LeandraChristine/voidnet_viator/3d_files/FDM/Optical_Mouse_Cover.stl

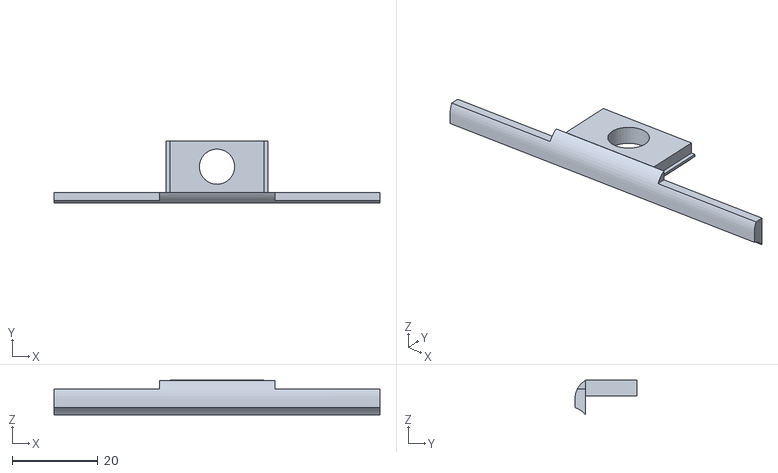
[picture p15: CAD file, 2022-09-26]
3d_files/FDM/Optical_Mouse_Cover.stl
76.0 x 14.5 x 8.09
