LeandraChristine/voidnet_viator/3d_files/FDM/Optical_Mouse_Casing.stl

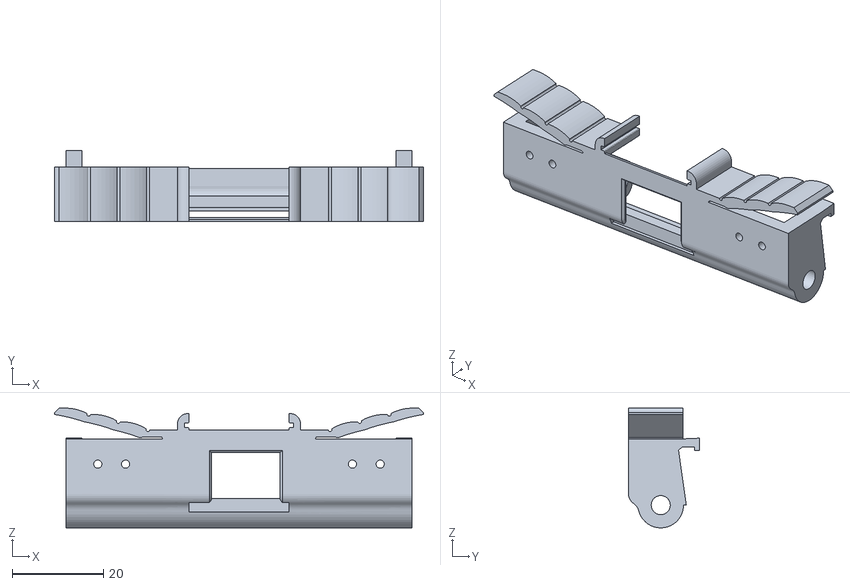
[picture p16: CAD file, 2022-09-26]
3d_files/FDM/Optical_Mouse_Casing.stl
81.0 x 15.6 x 26.3
