LeandraChristine/voidnet_viator/3d_files/FDM/Backplate_1.stl

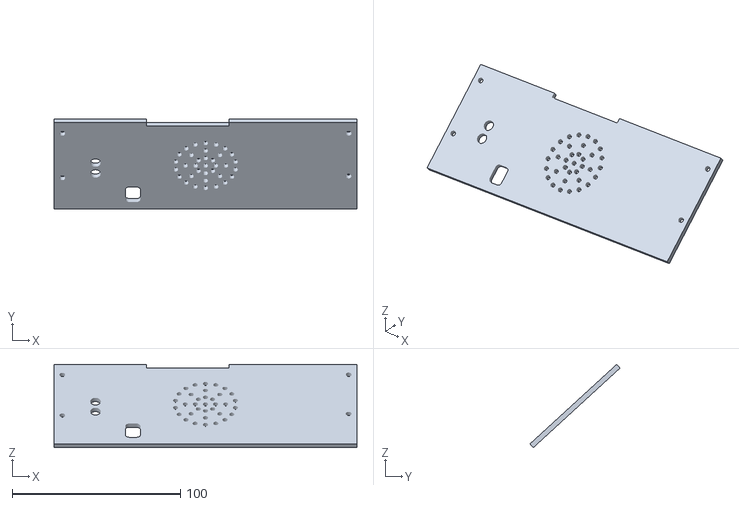
[picture p17: CAD file, 2022-09-26]
3d_files/FDM/Backplate_1.stl
179.9 x 53.5 x 49.4
