LeandraChristine/voidnet_viator/3d_files/FDM/Extension_Top.stl

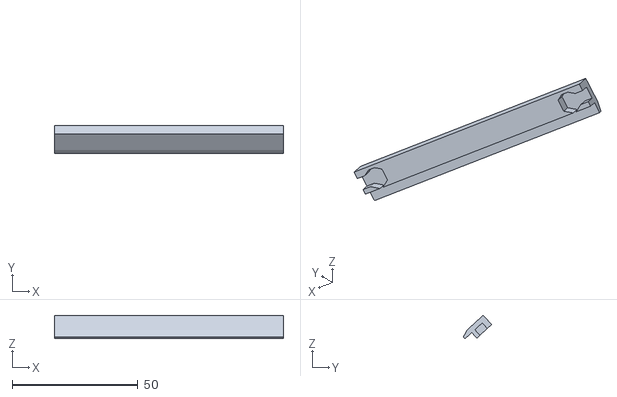
[picture p18: CAD file, 2022-09-26]
3d_files/FDM/Extension_Top.stl
91.2 x 11.3 x 9.35
