LeandraChristine/voidnet_viator/3d_files/FDM/Grip_Holder_Back.stl

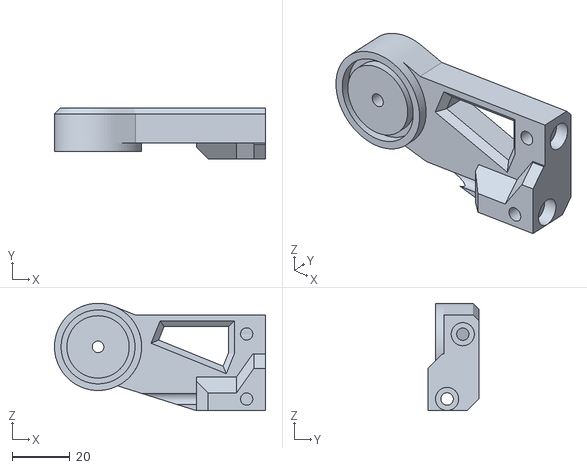
[picture p19: CAD file, 2022-09-26]
3d_files/FDM/Grip_Holder_Back.stl
72.8 x 17.5 x 37.0
