LeandraChristine/voidnet_viator/3d_files/FDM/Drillguide_Right.stl

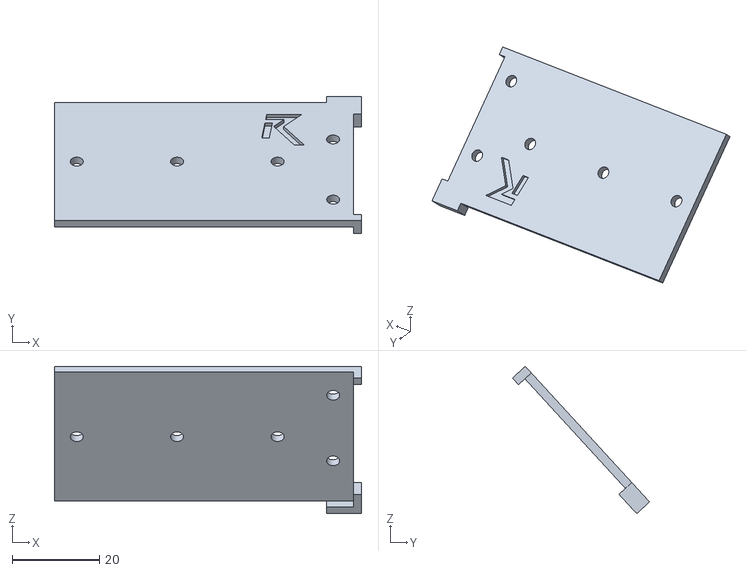
[picture p20: CAD file, 2022-09-26]
3d_files/FDM/Drillguide_Right.stl
70.2 x 31.4 x 33.7
