LeandraChristine/voidnet_viator/3d_files/FDM/Left_Front_Holder.stl

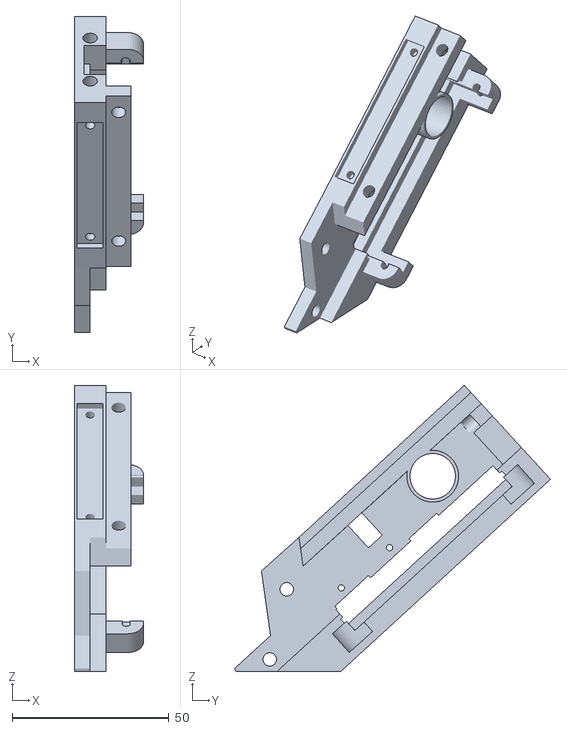
[picture p21: CAD file, 2022-09-26]
3d_files/FDM/Left_Front_Holder.stl
22.0 x 100.7 x 91.3
