LeandraChristine/voidnet_viator/3d_files/FDM/Back_Attachment_Left.stl

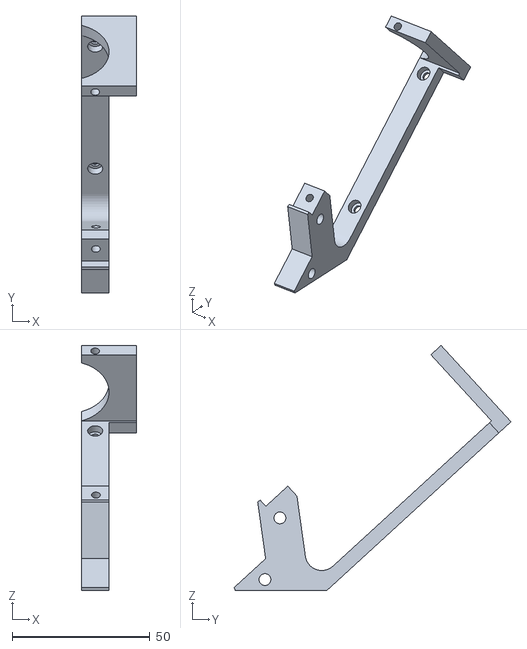
[picture p22: CAD file, 2022-09-26]
3d_files/FDM/Back_Attachment_Left.stl
20.0 x 100.4 x 88.8
