LeandraChristine/voidnet_viator/3d_files/FDM/Left_Panel.stl

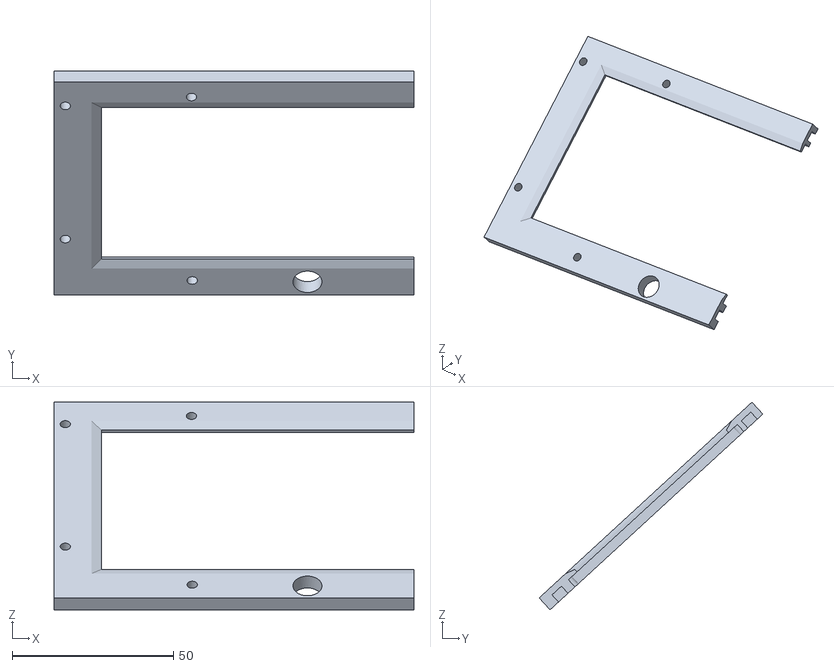
[picture p23: CAD file, 2022-09-26]
3d_files/FDM/Left_Panel.stl
111.5 x 69.3 x 64.3
