LeandraChristine/voidnet_viator/3d_files/FDM/Display_Panel.stl

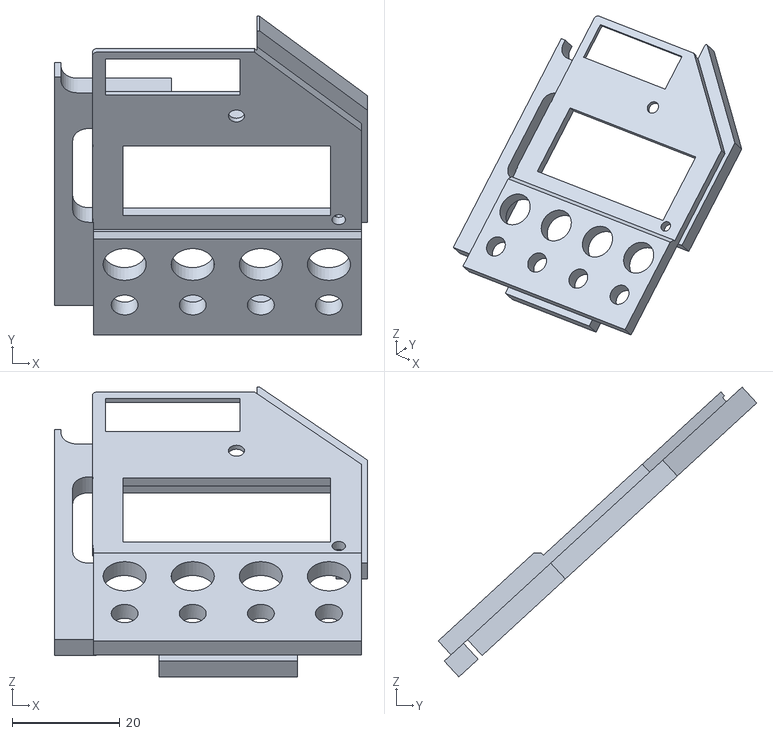
[picture p24: CAD file, 2022-09-26]
3d_files/FDM/Display_Panel.stl
58.0 x 59.0 x 53.7
