LeandraChristine/voidnet_viator/3d_files/FDM/Right_Panel.stl

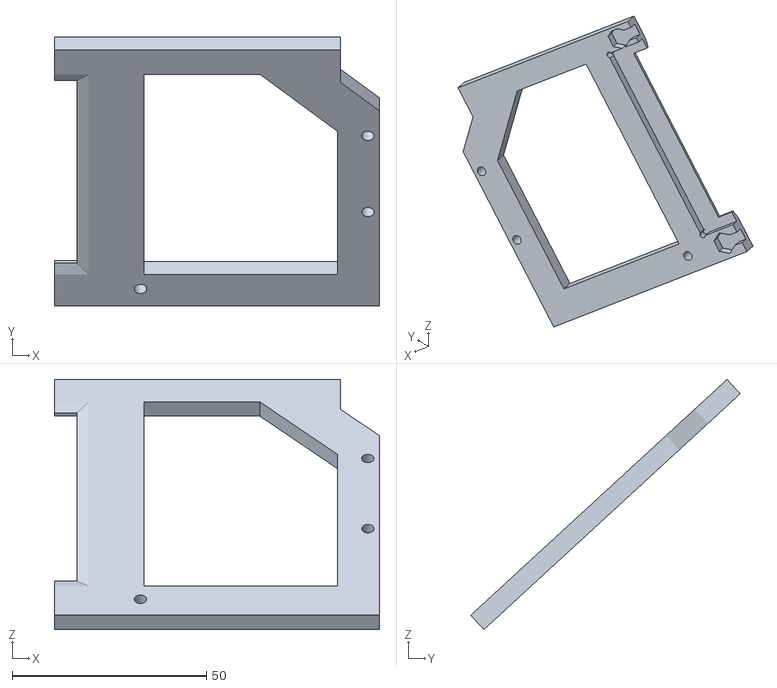
[picture p25: CAD file, 2022-09-26]
3d_files/FDM/Right_Panel.stl
83.6 x 69.3 x 64.3
