LeandraChristine/voidnet_viator/3d_files/FDM/Backplate_3.stl

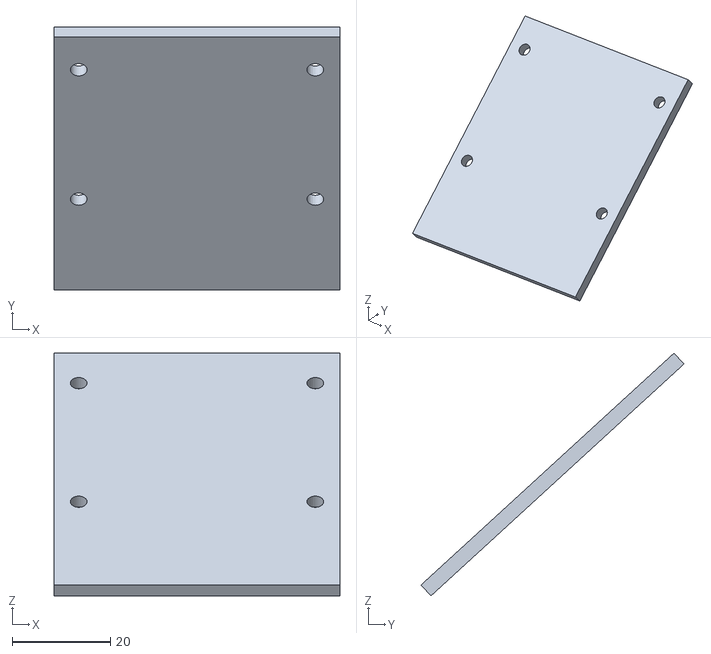
[picture p26: CAD file, 2022-09-26]
3d_files/FDM/Backplate_3.stl
58.2 x 53.5 x 49.4
