LeandraChristine/voidnet_viator/3d_files/FDM/Grip_Holder_Front.stl

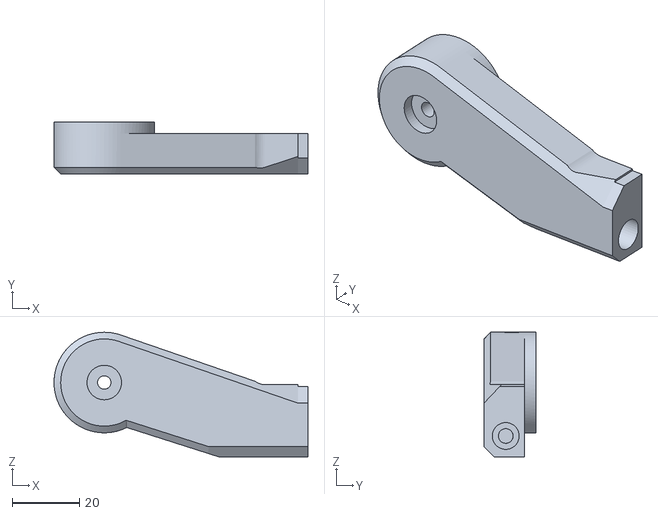
[picture p27: CAD file, 2022-09-26]
3d_files/FDM/Grip_Holder_Front.stl
75.7 x 15.5 x 37.1
