LeandraChristine/voidnet_viator/3d_files/FDM/FrontPanel_Clip.stl

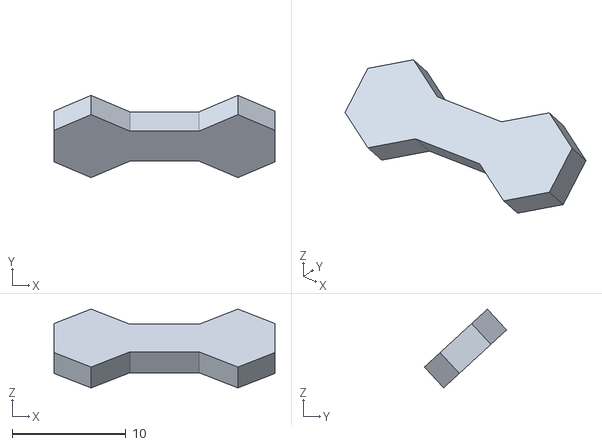
[picture p28: CAD file, 2022-09-26]
3d_files/FDM/FrontPanel_Clip.stl
19.5 x 7.24 x 6.94
