LeandraChristine/voidnet_viator/3d_files/FDM/Cable_Clamp_Top.stl

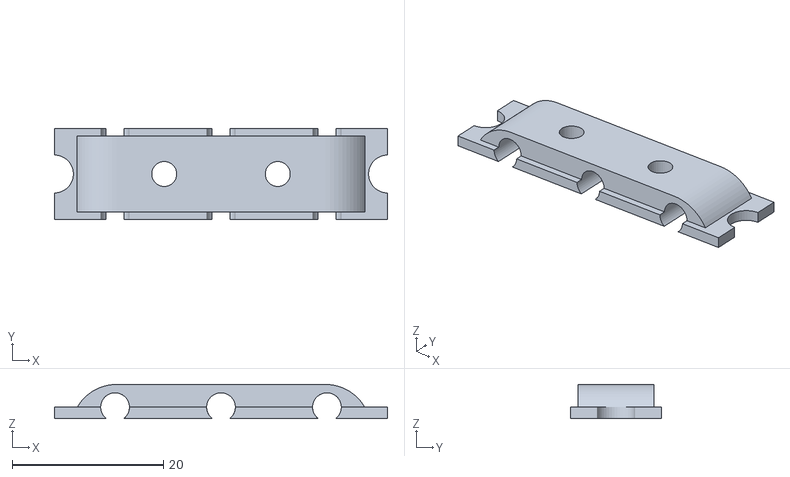
[picture p29: CAD file, 2022-09-26]
3d_files/FDM/Cable_Clamp_Top.stl
44.0 x 12.0 x 4.50
